JDi-5701/haptic_grasping_interface/models/SW/Assem3.SLDASM

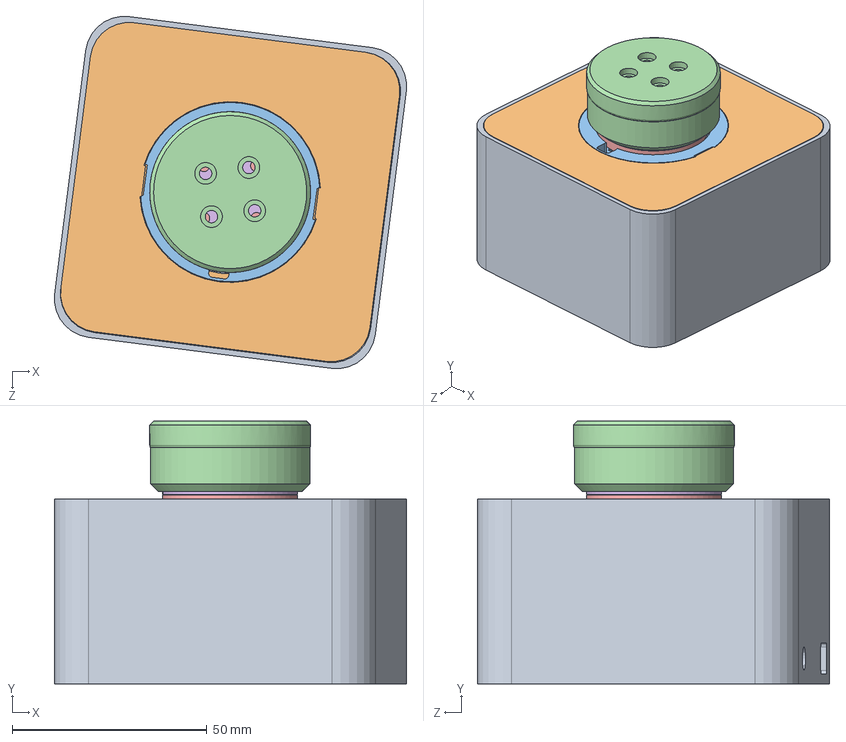
[picture p2: CAD file, 2024-08-28, last stored version]
models/SW/Assem3.SLDASM
90.4 x 67.5 x 90.4 mm
BLDCMotorTop
BLDMBottom
motor_lid
AS5600Connector
ControlBox_lid_rec
ControlBox_wall_rec
