JDi-5701/haptic_grasping_interface/models/SW/BLDCMotorAxis.SLDPRT

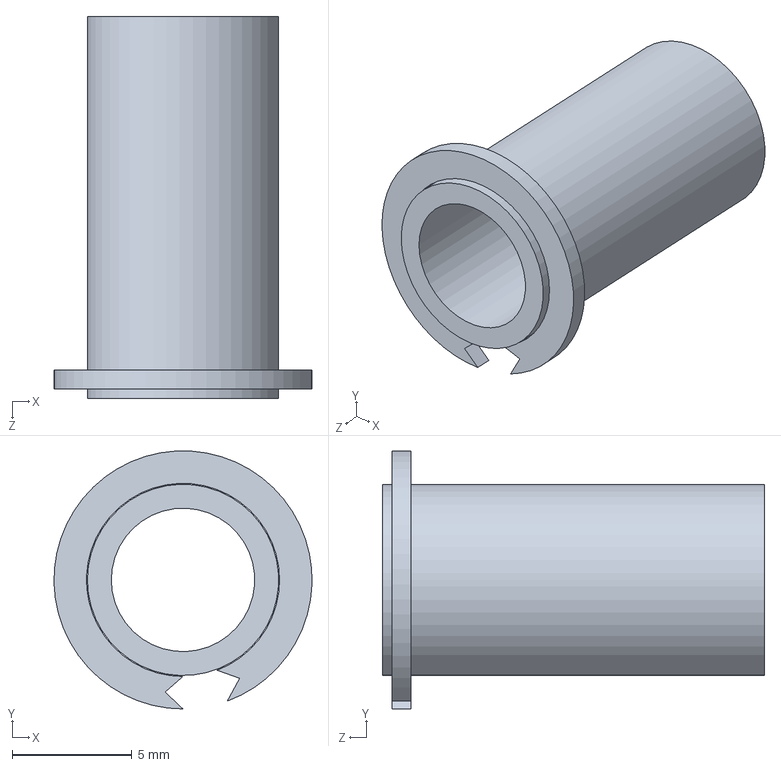
[picture p16: CAD file, 2024-08-28, last stored version]
models/SW/BLDCMotorAxis.SLDPRT
10.8 x 10.8 x 16.0 mm
