JDi-5701/haptic_grasping_interface/models/SW/MagnetHolder.SLDPRT

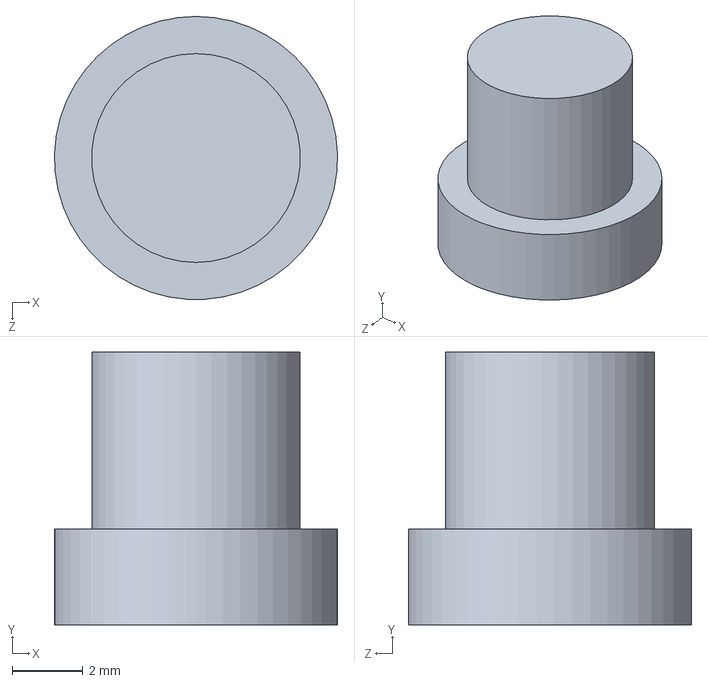
[picture p17: CAD file, 2024-08-28, last stored version]
models/SW/MagnetHolder.SLDPRT
8.00 x 7.70 x 8.00 mm
