JDi-5701/haptic_grasping_interface/models/SW/MotorTray.SLDPRT

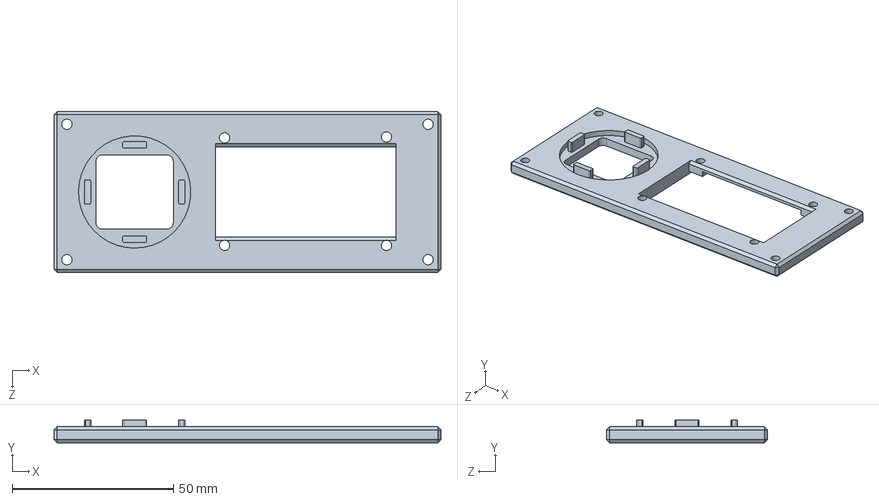
[picture p18: CAD file, 2024-08-28, last stored version]
models/SW/MotorTray.SLDPRT
120.0 x 7.00 x 50.0 mm
