JDi-5701/haptic_grasping_interface/models/SW/KnobButtom.SLDPRT

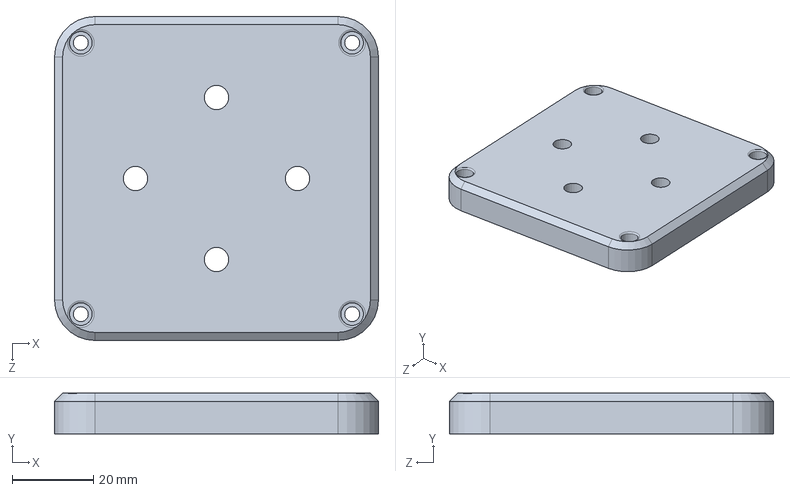
[picture p19: CAD file, 2024-08-28, last stored version]
models/SW/KnobButtom.SLDPRT
80.0 x 10.0 x 80.0 mm
