JDi-5701/haptic_grasping_interface/models/SW/KnobBase.SLDPRT

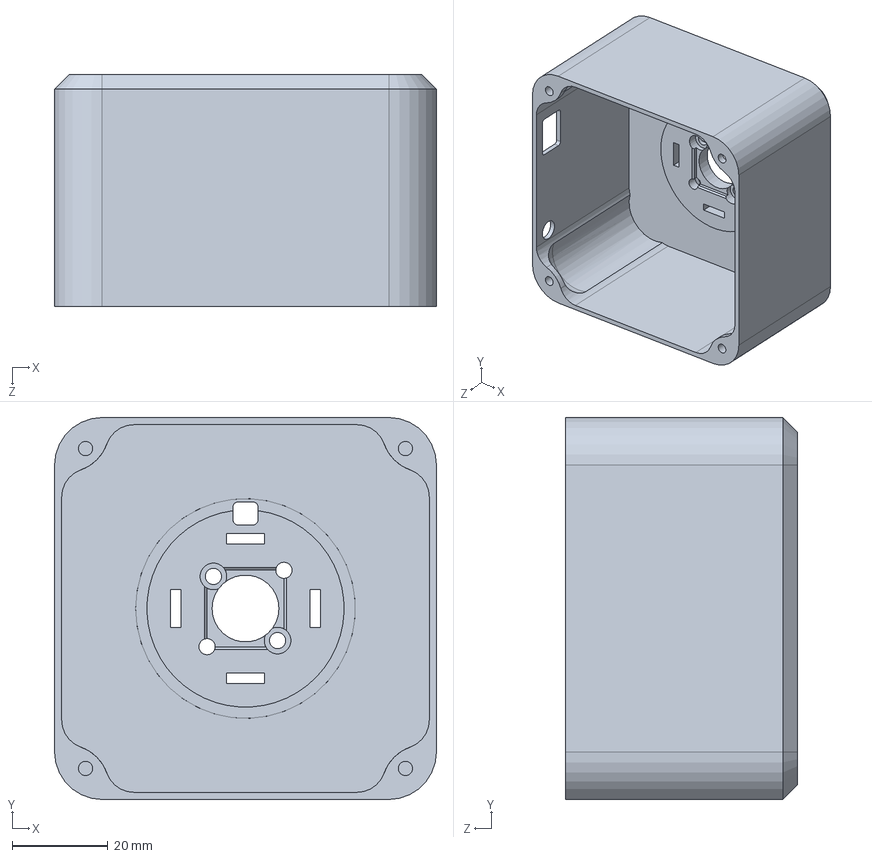
[picture p20: CAD file, 2024-08-28, last stored version]
models/SW/KnobBase.SLDPRT
80.0 x 80.0 x 48.5 mm
