JDi-5701/haptic_grasping_interface/models/SW/BLDCMotorTop.SLDPRT

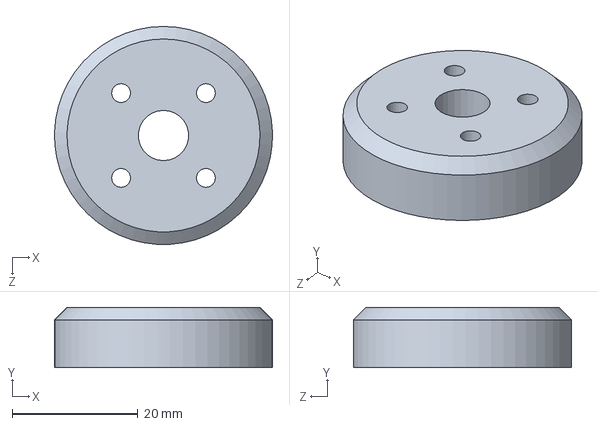
[picture p21: CAD file, 2024-08-28, last stored version]
models/SW/BLDCMotorTop.SLDPRT
34.7 x 9.60 x 34.7 mm
