JDi-5701/haptic_grasping_interface/models/SW/TrayFoot.SLDPRT

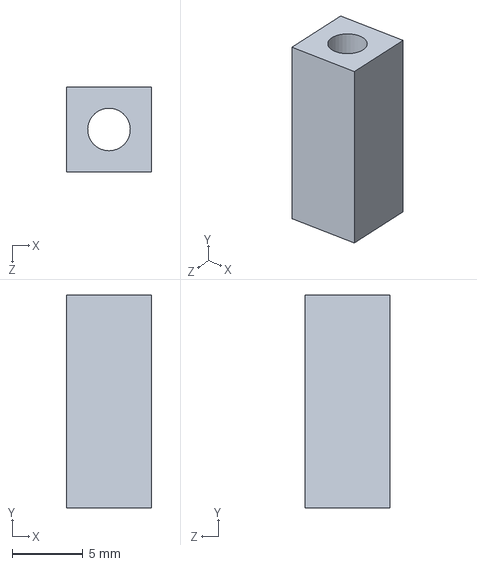
[picture p22: CAD file, 2024-08-28, last stored version]
models/SW/TrayFoot.SLDPRT
6.00 x 15.0 x 6.00 mm
