JDi-5701/haptic_grasping_interface/models/SW/ControlBox_wall_rec.SLDPRT

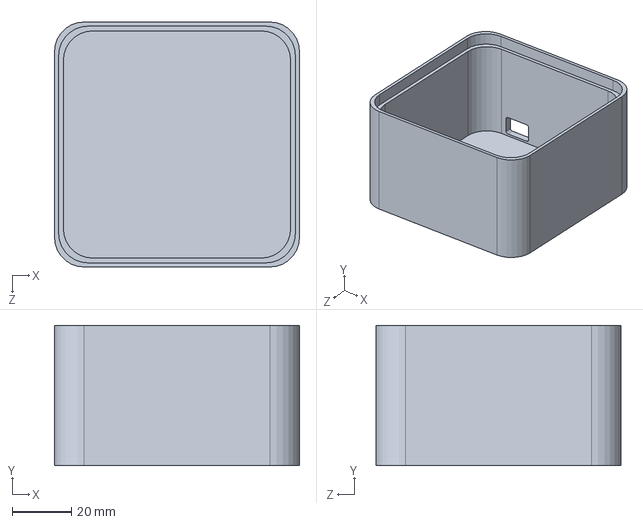
[picture p23: CAD file, 2024-08-28, last stored version]
models/SW/ControlBox_wall_rec.SLDPRT
83.0 x 47.5 x 83.0 mm
