JDi-5701/haptic_grasping_interface/models/SW/Fake_FT_sensor.SLDPRT

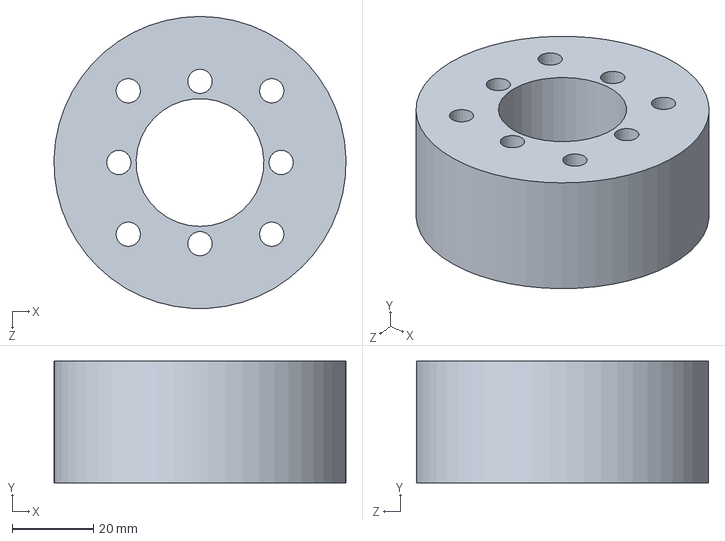
[picture p24: CAD file, 2024-08-28, last stored version]
models/SW/Fake_FT_sensor.SLDPRT
72.0 x 30.0 x 72.0 mm
