JDi-5701/haptic_grasping_interface/models/SW/ControlBox_buttom_rec.SLDPRT

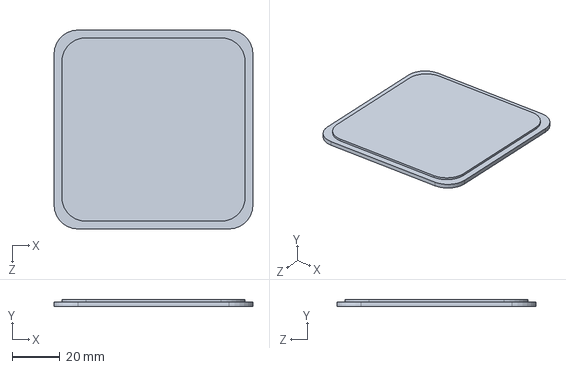
[picture p25: CAD file, 2024-08-28, last stored version]
models/SW/ControlBox_buttom_rec.SLDPRT
83.0 x 3.00 x 83.0 mm
