JDi-5701/haptic_grasping_interface/models/SW/ControlBox_buttom.SLDPRT

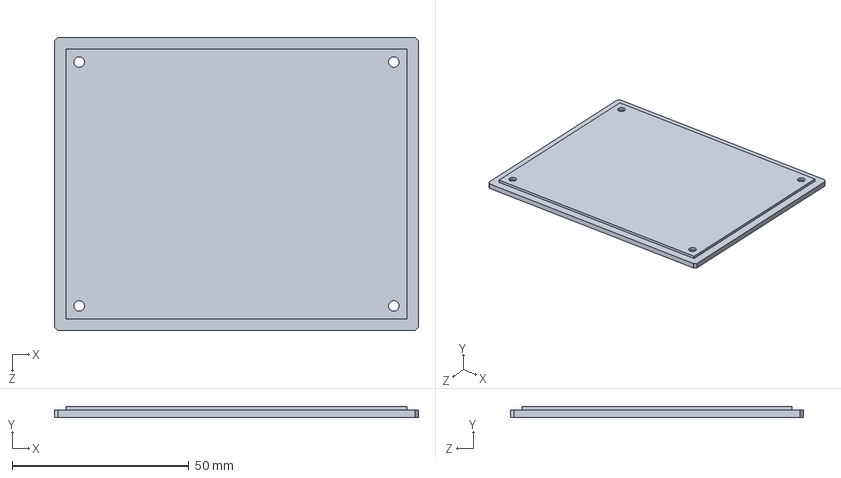
[picture p26: CAD file, 2024-08-28, last stored version]
models/SW/ControlBox_buttom.SLDPRT
103.0 x 3.00 x 83.0 mm
