JDi-5701/haptic_grasping_interface/models/SW/ControlBox_lid.SLDPRT

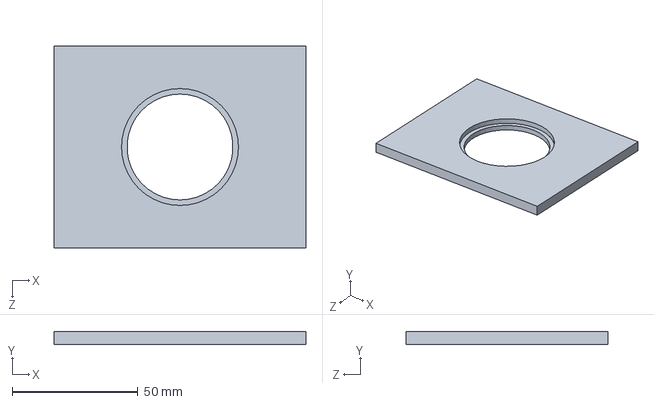
[picture p27: CAD file, 2024-08-28, last stored version]
models/SW/ControlBox_lid.SLDPRT
100.0 x 5.00 x 80.0 mm
