JDi-5701/haptic_grasping_interface/models/SW/AS5600Base.SLDPRT

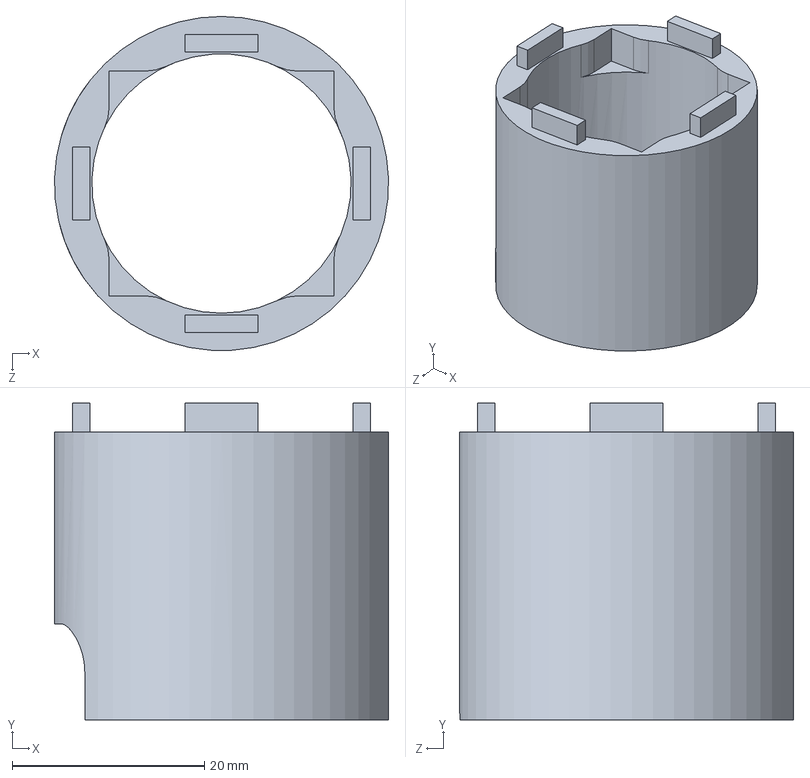
[picture p28: CAD file, 2024-08-28, last stored version]
models/SW/AS5600Base.SLDPRT
34.8 x 33.0 x 34.8 mm
