JDi-5701/haptic_grasping_interface/models/SW/AS5600.SLDPRT

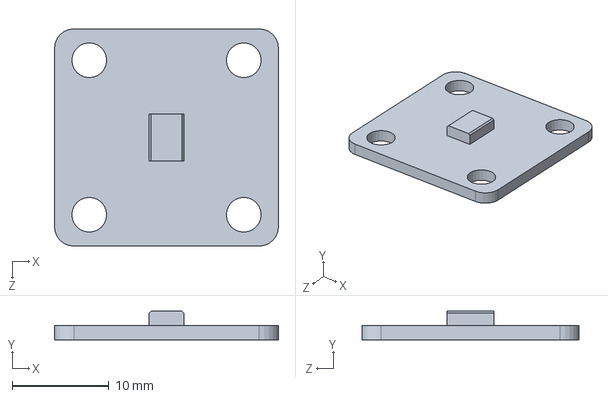
[picture p29: CAD file, 2024-08-28, last stored version]
models/SW/AS5600.SLDPRT
23.2 x 3.00 x 22.5 mm
