JDi-5701/haptic_grasping_interface/models/SW/BLDMBottom.SLDPRT

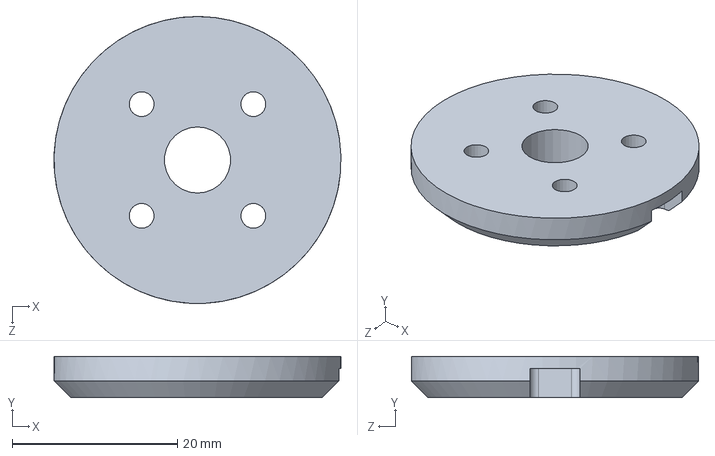
[picture p30: CAD file, 2024-08-28, last stored version]
models/SW/BLDMBottom.SLDPRT
34.7 x 5.00 x 34.7 mm
