JDi-5701/haptic_grasping_interface/models/SW/Fortiss_knob_v2.0.SLDASM

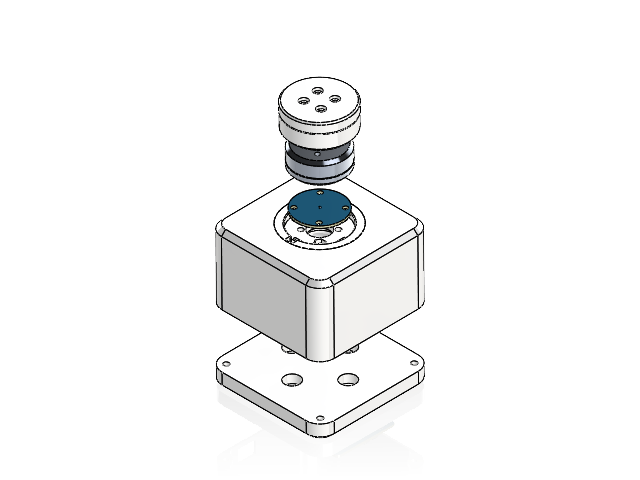
[picture p31: CAD file, 2024-08-28, last stored version]
models/SW/Fortiss_knob_v2.0.SLDASM
KnobBase
BLDMBottom
BLDCMotorTop
KnobButtom
motor_lid
COMPOUND.step x 3
SOLID.step
SOIC-8_L5.0-W4.0-P1.27-LS6.0-BL.step
Board.step
COMPOUND_1.step x 23
COMPOUND-0.step x 2
WQFN-28_L5.0-W5.0-P0.50-BL-EP3.2.step
COMPOUND-1.step x 3
COMPOUND-2.step x 2
SOLID_1.step x 23
USB-C-SMD_TYPE-C-6PIN-2MD-073.step
COMPOUND-3.step x 2
SOIC-8_L5.0-W4.0-P1.27-LS6.0-BL_1.step
SOIC-8_L5.0-W4.0-P1.27-LS6.0-BL-EP2.0.step
COMPOUND-4.step
SOLID-5.step x 2
COMPOUND-6.step
COMPOUND-7.step
SOLID-8.step
SOLID-9.step
COMPOUND-10.step
SOLID-11.step x 6
COMPOUND-12.step x 2
COMPOUND-13.step x 2
Board_1.step
